BorisFR/FourthInARow/modelisation/openscad Boris/dxf/grille_led.dxf

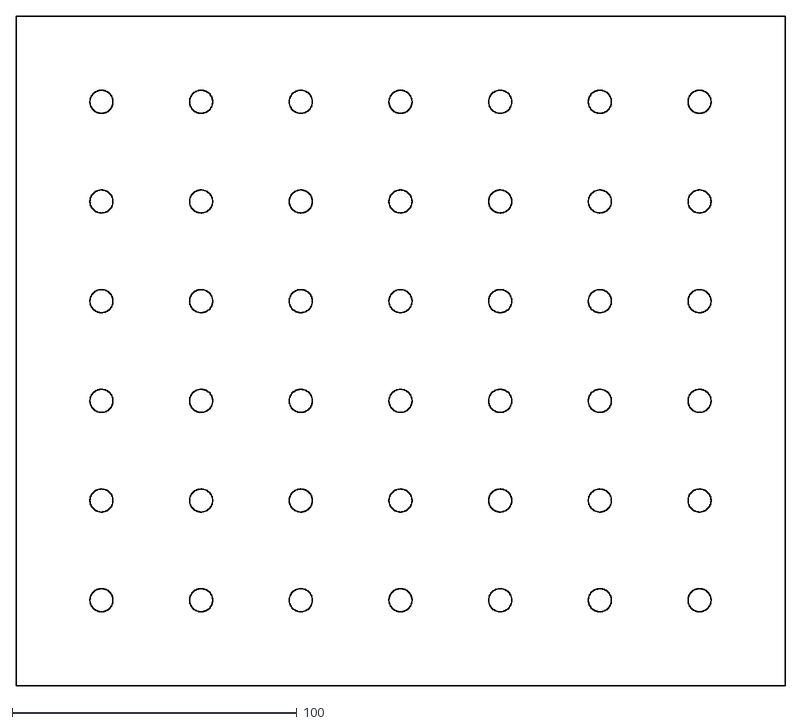
[picture p20: CAD file, 2018-02-16, an earlier design]
modelisation/openscad Boris/dxf/grille_led.dxf
270.0 x 235.0
