BorisFR/FourthInARow/modelisation/openscad Boris/logo_club_forme.scad

// Module names are of the form poly_<inkscape-path-id>().  As a result,
// you can associate a polygon in this OpenSCAD program with the corresponding
// SVG element in the Inkscape document by looking for the XML element with
// the attribute id="inkscape-path-id".

// fudge value is used to ensure that subtracted solids are a tad taller
// in the z dimension than the polygon being subtracted from.  This helps
// keep the resulting .stl file manifold.
fudge = 0.1;

module poly_path4018(h)
{
  scale([25.4/90, -25.4/90, 1]) union()
  {
    linear_extrude(height=h)
      polygon([[90.659249,289.750661],[83.343842,288.992171],[76.579249,287.989571],[70.709028,286.610592],[68.141889,285.798806],[65.829039,284.908071],[62.908844,283.478431],[60.658164,281.934383],[58.979457,280.194394],[57.775179,278.176931],[57.151487,276.374200],[57.165849,274.378051],[57.683533,271.892219],[58.831347,269.317445],[60.700641,266.490165],[63.382769,263.246821],[65.719446,260.991102],[68.435223,258.995745],[71.358545,257.370885],[74.317859,256.226661],[76.376701,255.835436],[78.798217,255.727687],[81.344446,255.900305],[83.777429,256.350181],[86.680459,257.259658],[90.148629,258.548171],[94.282923,260.134263],[95.939330,260.624558],[97.598753,260.954702],[101.757177,261.259585],[108.419249,261.299011],[115.968636,261.189759],[122.575564,260.829745],[129.224336,260.141100],[136.899249,259.045961],[148.563741,256.931576],[159.470724,254.418937],[164.250704,253.113584],[168.373971,251.829042],[171.684745,250.605436],[174.027249,249.482891],[175.594909,248.368684],[177.086468,246.950220],[178.374152,245.365561],[179.330189,243.752771],[180.052963,241.887816],[180.438091,240.013463],[180.473573,238.080083],[180.147404,236.038042],[179.447584,233.837711],[178.362110,231.429458],[176.878979,228.763651],[174.986189,225.790661],[172.495477,222.231457],[169.781913,218.710319],[166.712616,215.088056],[163.154702,211.225476],[158.975290,206.983389],[154.041499,202.222603],[141.379249,190.588171],[130.193118,180.442460],[122.048123,172.813290],[114.975124,165.806894],[107.004979,157.529511],[92.708942,142.381291],[89.394781,138.695880],[87.069869,135.903401],[84.101231,131.984351],[81.236209,127.769048],[78.493955,123.293912],[75.893621,118.595362],[73.454356,113.709819],[71.195314,108.673703],[69.135644,103.523433],[67.294499,98.295431],[64.587242,89.359380],[61.715809,78.946991],[57.426673,61.076893],[53.704769,43.550671],[50.494949,28.021741],[48.968799,20.854952],[47.926591,14.491880],[47.329637,8.644340],[47.139249,3.024151],[47.221507,-0.681781],[47.470524,-4.126965],[47.889664,-7.344962],[48.482289,-10.369329],[49.167555,-12.973382],[49.979547,-15.416424],[50.916883,-17.695960],[51.978182,-19.809490],[53.162061,-21.754519],[54.467140,-23.528548],[55.892037,-25.129081],[57.435369,-26.553619],[59.831899,-28.403899],[62.441719,-30.183412],[64.897340,-31.656209],[66.831269,-32.586339],[68.062552,-32.971919],[69.225812,-33.184883],[70.313376,-33.226918],[71.317573,-33.099713],[72.230731,-32.804955],[73.045177,-32.344333],[73.753241,-31.719535],[74.347249,-30.932249],[75.244232,-29.141969],[75.771532,-26.671264],[76.069006,-22.372194],[76.276509,-15.096819],[76.883849,0.903181],[77.572240,8.734361],[78.398460,16.265981],[79.364191,23.507788],[80.471117,30.469525],[81.720918,37.160937],[83.115278,43.591768],[84.655877,49.771765],[86.344399,55.710671],[89.116881,64.178674],[92.094157,71.922100],[95.321193,79.048738],[98.842959,85.666381],[102.053840,90.680658],[107.831329,99.337277],[119.736179,116.670671],[123.070229,121.208504],[126.568351,125.630126],[130.452985,130.170657],[134.946572,135.065216],[140.271552,140.548922],[146.650364,146.856896],[163.459249,162.886121],[172.306503,171.297117],[179.909778,178.727462],[186.415358,185.339241],[191.969524,191.294536],[196.718558,196.755431],[200.808740,201.884010],[204.386354,206.842355],[207.597679,211.792551],[210.071622,216.212622],[212.185068,220.779437],[213.808260,225.181554],[214.811439,229.107531],[215.094776,231.642732],[215.163992,234.597188],[215.024891,237.485184],[214.683279,239.821001],[213.888508,242.552279],[212.740158,245.624268],[211.398081,248.645847],[210.022129,251.225891],[207.874665,254.446833],[205.357213,257.588299],[202.486666,260.635848],[199.279917,263.575041],[195.753858,266.391436],[191.925382,269.070593],[187.811382,271.598072],[183.428749,273.959431],[178.625507,276.219177],[173.496670,278.324314],[168.063187,280.268783],[162.346006,282.046526],[156.366073,283.651484],[150.144338,285.077598],[143.701747,286.318810],[137.059249,287.369061],[128.719403,288.428815],[120.856089,289.147120],[112.734356,289.576762],[103.619249,289.770531],[90.659249,289.750731]]);
    linear_extrude(height=h)
      polygon([[-191.260751,268.290151],[-196.902168,267.581342],[-202.620751,266.533031],[-206.786479,265.378407],[-210.820609,263.885676],[-214.594811,262.108575],[-217.980751,260.100841],[-220.135751,258.376568],[-222.620751,256.033381],[-224.457875,253.986072],[-226.064751,251.833418],[-227.449300,249.556864],[-228.619441,247.137858],[-229.583091,244.557847],[-230.348171,241.798278],[-230.922600,238.840597],[-231.314296,235.666251],[-231.510054,231.855976],[-231.136432,228.306251],[-230.430274,224.556853],[-229.432567,220.434277],[-228.223772,216.241735],[-226.884351,212.282441],[-225.054672,207.859900],[-222.754797,202.927021],[-220.579551,198.768730],[-218.260245,194.754812],[-215.785016,190.869090],[-213.141997,187.095390],[-210.319323,183.417535],[-207.305131,179.819351],[-204.087554,176.284661],[-200.654729,172.797291],[-168.460751,143.098191],[-148.403251,124.658812],[-140.060751,116.816491],[-143.593631,108.533008],[-150.058361,94.110671],[-155.385170,83.070671],[-157.369777,78.894427],[-158.470117,76.043441],[-158.803941,73.799691],[-158.945650,71.083441],[-159.018135,68.821892],[-159.185650,67.671401],[-159.858957,67.063558],[-161.247299,66.145760],[-165.811063,63.571122],[-172.160896,60.329121],[-179.580751,56.801391],[-183.824143,54.676453],[-185.078370,53.811076],[-186.180005,52.820271],[-187.695377,51.078496],[-188.075374,50.318631],[-188.321666,49.446761],[-188.491488,47.983218],[-188.345766,46.506958],[-187.862406,44.910058],[-187.019317,43.084591],[-186.250592,41.876663],[-184.973757,40.312521],[-180.235778,35.364491],[-175.040036,30.368521],[-173.513174,29.208651],[-172.059973,28.394991],[-169.738114,27.452678],[-167.530373,26.858891],[-165.231276,26.676108],[-162.411148,27.013421],[-157.602646,28.053565],[-154.783414,28.921121],[-151.218304,30.196612],[-140.442784,34.500238],[-122.460751,42.022121],[-80.371522,59.632586],[-53.180751,70.832621],[-35.420751,77.897521],[-17.783759,84.775288],[-11.902779,86.916961],[-7.167961,88.498571],[-2.854636,90.011714],[0.754348,91.604912],[3.651700,93.274507],[5.830129,95.016841],[7.362626,96.721747],[8.441829,98.271471],[9.046006,99.909720],[9.208739,102.125191],[9.177520,103.483288],[9.021331,104.534915],[8.666626,105.581679],[8.039859,106.925191],[7.118134,108.538414],[5.950297,110.172950],[4.572139,111.794919],[3.019453,113.370443],[1.328029,114.865646],[-0.466340,116.246648],[-2.327864,117.479573],[-4.220751,118.530541],[-6.855241,119.734950],[-9.175447,120.429288],[-11.818305,120.742915],[-15.420751,120.805191],[-20.179151,120.643697],[-21.723836,120.376770],[-23.420751,119.906091],[-27.096784,118.674275],[-30.845216,117.151826],[-35.089383,115.152190],[-40.252621,112.488811],[-44.893341,110.127679],[-50.630289,107.436042],[-69.340751,99.266731],[-104.510294,84.409603],[-113.057557,81.031994],[-115.492119,80.184023],[-116.860751,79.831121],[-117.568399,79.768900],[-118.085153,79.851620],[-118.547244,80.129472],[-119.090901,80.652651],[-119.590440,81.248016],[-119.895176,81.853772],[-120.159451,83.801391],[-120.047693,86.403385],[-119.455411,89.950671],[-117.817001,98.394281],[-117.043744,101.990445],[-116.330481,104.396591],[-115.525953,105.788028],[-114.533281,106.944551],[-112.867962,108.113303],[-110.699113,108.945046],[-107.549216,109.570621],[-102.940751,110.120871],[-93.863695,111.199373],[-84.269111,112.628370],[-74.690974,114.320922],[-65.663261,116.190091],[-57.409072,118.236127],[-50.829173,120.304072],[-48.100953,121.370200],[-45.711951,122.470531],[-43.635714,123.614643],[-41.845791,124.812111],[-39.027702,127.203567],[-36.566451,129.894250],[-34.584037,132.732365],[-33.202461,135.566121],[-32.642605,137.509333],[-32.279758,139.708807],[-32.141060,141.925556],[-32.253651,143.920591],[-32.686019,145.954015],[-33.346471,148.076651],[-34.364692,150.348992],[-35.658884,152.615242],[-37.052945,154.597124],[-38.370771,156.016361],[-39.826912,157.022448],[-41.475361,157.855661],[-42.525818,158.215924],[-43.615796,158.430717],[-46.940751,158.555271],[-50.375507,158.394233],[-53.197161,157.857161],[-57.309769,156.517611],[-61.772877,154.618911],[-66.452115,152.224168],[-71.213111,149.396491],[-73.828489,147.827155],[-76.388858,146.541945],[-79.413264,145.306600],[-83.420751,143.886861],[-89.504063,141.978396],[-94.830043,140.713768],[-100.023383,139.973942],[-105.708771,139.639881],[-111.270931,139.613212],[-115.148771,140.014831],[-118.016579,140.599324],[-120.890771,141.390535],[-123.579757,142.328901],[-125.891951,143.354861],[-129.715751,145.683911],[-135.247086,150.458556],[-147.297728,161.274092],[-181.482809,192.466021],[-191.124186,201.497127],[-196.304857,206.646541],[-198.408734,209.300108],[-200.235262,211.911253],[-201.767386,214.442277],[-202.988054,216.855481],[-203.880213,219.113164],[-204.426808,221.177629],[-204.610787,223.011174],[-204.415097,224.576101],[-204.062810,225.555784],[-203.574535,226.418130],[-202.942265,227.168638],[-202.157994,227.812808],[-201.213713,228.356142],[-200.101418,228.804141],[-197.340751,229.436131],[-192.786635,229.899863],[-185.908948,230.348257],[-169.526156,230.960931],[-161.529488,231.008047],[-154.331865,230.824040],[-147.807448,230.403368],[-141.830399,229.740491],[-137.945434,229.330632],[-134.611609,229.252555],[-131.707652,229.509741],[-129.112291,230.105671],[-127.194219,230.879766],[-125.594231,231.810731],[-124.341773,233.060040],[-123.260751,234.602051],[-122.711321,235.687118],[-122.426157,236.747628],[-122.304731,241.150661],[-122.442949,245.535166],[-122.666670,247.012659],[-123.041751,248.496231],[-123.891148,250.925278],[-124.903971,253.190691],[-126.267691,255.278678],[-128.047507,257.258537],[-130.059780,258.952363],[-132.120871,260.182251],[-135.192413,261.263197],[-139.740751,262.546921],[-145.551680,263.944120],[-151.303992,265.158679],[-156.976863,266.187783],[-162.549469,267.028617],[-168.000985,267.678364],[-173.310586,268.134209],[-178.457450,268.393337],[-183.420751,268.452931],[-191.260751,268.290151]]);
    linear_extrude(height=h)
      polygon([[-4.605071,78.609521],[-6.086199,77.715177],[-7.544956,76.464570],[-8.858130,74.979308],[-9.902511,73.381001],[-11.292486,69.823331],[-13.492731,63.390671],[-16.877551,53.520490],[-18.587616,49.095412],[-20.552451,44.459693],[-25.975435,32.904386],[-34.604511,15.550671],[-41.869837,0.909671],[-45.804901,-7.329329],[-49.076931,-15.784419],[-51.468055,-22.948140],[-53.562062,-30.245613],[-55.360248,-37.684160],[-56.863911,-45.271105],[-58.074346,-53.013772],[-58.992849,-60.919482],[-59.620719,-68.995561],[-59.959251,-77.249329],[-59.986778,-84.896922],[-59.641792,-91.334432],[-58.872601,-97.129390],[-57.627511,-102.849329],[-56.792764,-105.788147],[-55.796079,-108.717054],[-54.647718,-111.614782],[-53.357944,-114.460067],[-51.937022,-117.231640],[-50.395213,-119.908236],[-48.742782,-122.468588],[-46.989991,-124.891429],[-44.804214,-127.602145],[-42.502594,-130.178271],[-40.065854,-132.636464],[-37.474719,-134.993385],[-34.709917,-137.265694],[-31.752171,-139.470050],[-28.582207,-141.623111],[-25.180751,-143.741539],[-20.465883,-146.386236],[-15.701538,-148.719449],[-10.926690,-150.728782],[-6.180311,-152.401843],[-1.501373,-153.726235],[3.071149,-154.689565],[7.498284,-155.279438],[11.741059,-155.483459],[16.306525,-155.243490],[20.930606,-154.509804],[25.607775,-153.284681],[30.332508,-151.570403],[35.099278,-149.369251],[39.902559,-146.683505],[44.736824,-143.515448],[49.596549,-139.867359],[54.925458,-135.204368],[60.835269,-129.382949],[66.525721,-123.229228],[71.196549,-117.569329],[73.849417,-113.774652],[76.345202,-109.647828],[78.518977,-105.481754],[80.205819,-101.569329],[81.527524,-97.393061],[82.389917,-93.188595],[82.762084,-89.162032],[82.613109,-85.519469],[82.129858,-82.877307],[81.359581,-80.279073],[80.343643,-77.841405],[79.123409,-75.680939],[77.080796,-73.115053],[74.274899,-70.135939],[71.264714,-67.417474],[70.098936,-66.579631],[69.053189,-66.005389],[67.243982,-65.339469],[66.567263,-65.347863],[65.720089,-65.538689],[64.300099,-66.086751],[62.860802,-67.016556],[61.342854,-68.403272],[59.686912,-70.322065],[57.833630,-72.848102],[55.723666,-76.056549],[50.496309,-84.821339],[46.447898,-91.634132],[43.035341,-96.724849],[39.703215,-100.852634],[35.896099,-104.776629],[32.204144,-108.100959],[28.479516,-110.954840],[24.513967,-113.484049],[20.099249,-115.834359],[17.328969,-117.105719],[14.502480,-118.231419],[11.629355,-119.209003],[8.719168,-120.036014],[5.781491,-120.709995],[2.825897,-121.228489],[-0.138041,-121.589040],[-3.100751,-121.789189],[-7.399868,-121.828043],[-8.849163,-121.650264],[-10.400151,-121.303159],[-12.888981,-120.527360],[-15.138291,-119.606969],[-17.256247,-118.282555],[-19.429291,-116.535389],[-20.757486,-115.193658],[-21.980276,-113.723932],[-23.100110,-112.121643],[-24.119434,-110.382225],[-25.866348,-106.473731],[-27.240601,-101.961909],[-28.026349,-98.168683],[-28.581876,-94.050575],[-28.911802,-89.562667],[-29.020751,-84.660039],[-28.900709,-79.239432],[-28.551553,-73.663702],[-27.989739,-68.133463],[-27.231721,-62.849329],[-25.665164,-54.926970],[-24.703434,-51.239509],[-23.549146,-47.514193],[-22.147104,-43.585769],[-20.442115,-39.288984],[-15.902521,-28.929329],[-5.117601,-4.289329],[6.805266,23.126368],[13.381659,37.790671],[15.411253,42.365671],[16.840809,45.950671],[17.402922,47.675374],[17.702429,49.145085],[17.843359,53.950671],[17.710072,58.676031],[17.449848,60.098669],[16.977609,61.630671],[15.934452,64.199505],[14.642549,66.780751],[13.434713,68.714594],[12.035243,70.621031],[10.494016,72.451261],[8.860911,74.156486],[7.185804,75.687906],[5.518573,76.996721],[3.909096,78.034133],[2.407249,78.751341],[0.615696,79.241194],[-1.192469,79.379993],[-2.953855,79.169011],[-4.605071,78.609521]]);
    difference()
    {
       linear_extrude(height=h)
         polygon([[-224.743971,45.496561],[-225.730726,44.549601],[-226.615404,43.079426],[-227.290653,41.309041],[-227.649120,39.461451],[-227.677809,38.038916],[-227.531465,36.419854],[-226.748706,32.718738],[-225.370898,28.611284],[-223.468094,24.350671],[-209.559448,-2.952169],[-197.020751,-27.768439],[-197.715525,-28.033397],[-199.385941,-28.342619],[-201.341331,-28.731345],[-202.871243,-29.255605],[-203.891111,-29.877391],[-204.316370,-30.558689],[-202.013947,-35.759227],[-195.855681,-48.959066],[-177.011335,-88.766038],[-157.862776,-128.798390],[-151.324242,-142.279955],[-148.489445,-147.874909],[-147.420632,-149.182662],[-146.398466,-150.212629],[-145.087729,-151.145654],[-143.562060,-151.951152],[-141.943045,-152.573900],[-140.352268,-152.958679],[-138.377525,-153.089687],[-136.148111,-152.775389],[-133.770651,-152.289589],[-116.715021,-185.828189],[-104.074947,-210.520002],[-97.565111,-222.788304],[-94.336083,-227.691004],[-90.842982,-232.525153],[-87.112271,-237.261043],[-83.170412,-241.868965],[-79.043868,-246.319210],[-74.759101,-250.582070],[-70.342574,-254.627836],[-65.820751,-258.426799],[-59.613661,-263.146035],[-53.257027,-267.446896],[-46.662255,-271.385748],[-39.740751,-275.018952],[-34.871503,-277.330345],[-30.348153,-279.288701],[-25.881102,-281.012634],[-21.180751,-282.620760],[-14.250888,-284.729735],[-7.580751,-286.338521],[-2.505287,-287.363410],[2.646824,-288.223332],[7.864958,-288.917397],[13.138489,-289.444716],[18.456794,-289.804399],[23.809247,-289.995556],[29.185224,-290.017298],[34.574099,-289.868734],[41.352812,-289.458576],[47.822455,-288.825621],[54.022125,-287.961703],[59.990919,-286.858656],[65.767933,-285.508314],[71.392261,-283.902511],[76.903001,-282.033080],[82.339249,-279.891855],[86.656177,-277.946230],[90.896381,-275.782232],[95.038663,-273.414052],[99.061823,-270.855881],[102.944661,-268.121911],[106.665978,-265.226332],[110.204574,-262.183334],[113.539249,-259.007109],[116.550592,-255.867915],[119.361790,-252.691386],[121.994030,-249.447542],[124.468499,-246.106404],[126.806384,-242.637993],[129.028871,-239.012328],[131.157147,-235.199431],[133.212399,-231.169321],[136.905039,-223.009321],[139.230944,-216.540890],[141.332281,-209.618465],[143.134084,-202.511467],[144.561389,-195.489319],[145.798377,-186.998898],[146.680058,-177.743298],[147.174085,-168.165458],[147.248109,-158.708319],[147.139249,-151.847319],[150.339249,-150.427179],[169.087938,-141.851996],[186.547542,-133.375960],[201.767567,-125.475387],[208.240708,-121.889746],[213.797519,-118.626589],[219.556203,-114.943436],[224.988788,-111.174830],[229.232659,-107.944682],[230.639259,-106.726500],[231.425199,-105.876899],[231.639047,-105.507503],[231.672977,-105.204359],[231.126069,-104.435279],[230.235684,-103.777069],[229.141329,-103.308339],[227.935459,-103.147910],[226.839509,-103.551939],[222.458259,-106.637289],[218.063311,-109.820345],[213.062178,-113.189157],[207.486535,-116.725095],[201.368054,-120.409525],[187.629280,-128.149338],[172.099249,-136.259539],[155.777958,-144.248669],[149.754838,-147.045013],[147.081489,-148.129329],[146.802770,-147.800001],[146.572873,-147.027932],[146.458789,-146.136991],[146.527509,-145.451049],[147.596514,-144.765032],[149.950389,-143.679309],[159.840611,-139.321519],[170.713751,-134.189835],[181.182424,-128.957968],[189.859249,-124.299629],[198.337718,-119.316032],[205.808769,-114.529724],[212.485061,-109.797634],[218.579249,-104.976689],[220.653822,-103.147552],[221.681014,-101.908715],[221.846033,-101.427836],[221.802236,-100.995141],[221.158899,-100.141789],[220.414041,-99.680990],[219.606639,-99.489329],[219.003787,-99.658163],[218.041009,-100.157749],[215.106989,-102.107679],[207.869755,-107.094366],[199.787654,-112.288940],[191.143654,-117.515107],[182.220719,-122.596569],[168.877156,-129.642478],[162.336205,-132.841389],[155.667219,-135.932379],[145.297368,-140.499718],[142.855527,-141.447853],[141.964339,-141.621069],[141.885939,-141.310209],[147.779279,-138.548559],[157.251366,-133.937820],[168.259279,-128.030189],[177.856868,-122.581655],[188.384224,-116.409429],[197.078821,-111.155631],[201.178129,-108.462379],[201.525668,-107.974727],[201.547964,-107.561975],[201.264470,-107.276164],[200.694639,-107.169329],[199.093859,-107.861553],[196.153519,-109.525829],[184.216602,-116.267154],[166.944468,-125.572319],[150.391620,-134.226664],[144.276960,-137.305198],[140.612559,-139.015529],[136.965839,-140.503379],[134.112269,-140.076349],[132.100097,-139.680767],[131.269489,-139.329329],[134.170442,-137.736792],[141.129809,-134.357289],[153.715281,-128.179849],[164.635456,-122.300828],[174.232294,-116.525987],[178.641326,-113.616935],[182.847759,-110.661089],[187.117717,-107.500487],[190.513552,-104.807439],[193.576218,-102.132324],[196.846669,-99.025519],[199.757962,-96.082595],[201.995706,-93.616494],[203.432083,-91.777004],[203.939279,-90.713909],[203.800537,-90.290119],[203.466959,-90.007989],[202.120602,-90.397285],[199.546959,-91.587799],[192.556073,-94.903577],[190.198273,-95.841030],[189.173099,-96.051149],[189.138657,-95.323038],[189.409899,-93.926549],[189.705382,-92.474177],[189.729139,-91.611709],[189.437507,-91.299278],[188.974799,-91.169329],[187.156223,-92.028744],[183.604749,-94.094999],[176.859679,-98.121401],[169.909150,-102.079851],[162.768304,-105.962665],[155.452283,-109.762158],[147.976228,-113.470643],[140.355282,-117.080435],[132.604585,-120.583849],[124.739279,-123.973199],[112.257107,-129.029650],[107.629033,-130.788678],[105.651889,-131.420189],[107.009628,-130.510827],[110.717619,-128.472339],[117.698561,-124.671277],[122.737389,-121.671554],[125.791747,-119.500236],[126.561514,-118.733687],[126.819279,-118.184389],[126.763954,-117.843093],[126.408163,-117.757600],[125.467186,-118.070410],[123.656302,-118.924020],[116.285930,-122.823637],[102.019279,-130.596439],[89.219279,-137.587009],[80.419279,-140.437169],[64.728407,-145.384138],[50.400989,-149.548129],[36.946143,-153.153470],[22.722583,-156.676173],[8.242791,-159.994102],[-5.980751,-162.985119],[-19.512157,-165.534860],[-34.118172,-168.021905],[-48.255476,-170.195985],[-60.380751,-171.806829],[-66.700751,-172.623099],[-67.209251,-172.863373],[-67.420751,-173.218629],[-58.740624,-195.840173],[-49.739911,-218.449322],[-49.190588,-218.745739],[-47.924589,-218.814230],[-41.660321,-218.223136],[-36.508446,-217.537577],[-31.045423,-216.630998],[-25.268531,-215.502764],[-19.175047,-214.152238],[-6.027415,-210.781765],[8.419249,-206.514487],[19.235007,-203.012248],[30.378827,-199.158708],[41.863338,-194.948872],[53.701171,-190.377745],[65.904953,-185.440334],[78.487314,-180.131642],[91.460883,-174.446676],[104.838289,-168.380439],[112.982072,-164.702477],[116.470349,-163.273749],[116.528399,-163.499695],[116.425049,-163.799929],[115.112909,-164.622751],[111.859096,-166.327222],[101.324892,-171.514144],[88.419319,-177.626761],[76.739259,-182.931139],[64.605827,-188.120611],[52.714715,-192.954539],[41.072397,-197.430661],[29.685346,-201.546714],[18.560033,-205.300434],[7.702933,-208.689560],[-2.879483,-211.711828],[-13.180741,-214.364976],[-21.801165,-216.364172],[-29.685213,-217.986226],[-37.070988,-219.276552],[-44.196591,-220.280560],[-46.988388,-220.711091],[-48.342151,-221.082733],[-48.470427,-221.662052],[-48.171391,-222.770883],[-47.670911,-224.129321],[-44.825821,-224.089021],[-41.933676,-223.931103],[-38.271939,-223.529554],[-28.700741,-222.003459],[-16.972318,-219.584230],[-4.531315,-216.465198],[8.533952,-212.676594],[22.135166,-208.248652],[36.184007,-203.211604],[50.592160,-197.595680],[65.271307,-191.431115],[80.133129,-184.748139],[102.823929,-173.726979],[116.338299,-166.968309],[116.112379,-169.468819],[115.683527,-172.972467],[114.999314,-177.168830],[113.250399,-185.482229],[112.026848,-189.863485],[110.518139,-194.537691],[108.880911,-199.047564],[107.271799,-202.935825],[104.778906,-208.009948],[101.907077,-213.067991],[98.820976,-217.838326],[95.685269,-222.049322],[92.558750,-225.657479],[88.997893,-229.320774],[85.204219,-232.842340],[81.379249,-236.025311],[75.961516,-239.795652],[69.859249,-243.421260],[64.142880,-246.238167],[58.093947,-248.734458],[51.746429,-250.901762],[45.134306,-252.731711],[38.291556,-254.215935],[31.252159,-255.346064],[24.050094,-256.113729],[16.719339,-256.510559],[10.639326,-256.557657],[6.159339,-256.316220],[0.445535,-255.568102],[-5.262296,-254.544004],[-10.932126,-253.253569],[-16.531929,-251.706440],[-22.029680,-249.912260],[-27.393351,-247.880671],[-32.590917,-245.621317],[-37.590351,-243.143839],[-41.980407,-240.715981],[-46.182717,-238.167374],[-50.216020,-235.483711],[-54.099054,-232.650682],[-57.850559,-229.653978],[-61.489273,-226.479290],[-65.033934,-223.112309],[-68.503281,-219.538726],[-72.184086,-215.414461],[-75.679057,-211.122527],[-78.993252,-206.655056],[-82.131733,-202.004182],[-85.099560,-197.162039],[-87.901794,-192.120758],[-90.543494,-186.872474],[-93.029721,-181.409319],[-97.808525,-171.449987],[-110.306365,-146.236039],[-166.585193,-33.729329],[-191.103189,15.529861],[-194.455183,22.104948],[-197.957511,27.895282],[-201.646553,32.955755],[-203.572460,35.229448],[-205.558687,37.341261],[-207.948654,39.570993],[-210.415969,41.544053],[-212.839153,43.171022],[-215.096729,44.362481],[-216.820404,44.978156],[-218.949134,45.541081],[-221.049293,45.951456],[-222.687260,46.109481],[-223.725984,45.929186],[-224.743971,45.496561]]);
       translate([0, 0, -fudge])
         linear_extrude(height=h+2*fudge)
           polygon([[-33.807201,-175.619209],[-31.996744,-176.539274],[-30.134471,-177.815589],[-27.925699,-179.894569],[-26.129327,-182.247780],[-24.730847,-184.897941],[-23.715751,-187.867769],[-23.336818,-190.105987],[-23.180122,-192.811205],[-23.253003,-195.510092],[-23.562801,-197.729322],[-24.026418,-199.278867],[-24.669641,-200.811841],[-25.468185,-202.295081],[-26.397766,-203.695423],[-27.434098,-204.979704],[-28.552896,-206.114761],[-29.729875,-207.067430],[-30.940751,-207.804548],[-32.599198,-208.482311],[-34.408104,-208.934674],[-36.256526,-209.141636],[-38.033521,-209.083197],[-39.875374,-208.664878],[-41.896376,-207.868133],[-43.876653,-206.795676],[-45.596331,-205.550221],[-46.733962,-204.404275],[-47.938267,-202.898937],[-49.084524,-201.204016],[-50.048011,-199.489322],[-50.763367,-197.685098],[-51.314508,-195.538123],[-51.669476,-193.206361],[-51.796311,-190.847779],[-51.709434,-188.806070],[-51.447158,-186.865798],[-51.012637,-185.034560],[-50.409024,-183.319957],[-49.639476,-181.729586],[-48.707146,-180.271047],[-47.615190,-178.951938],[-46.366761,-177.779859],[-45.081248,-176.806861],[-43.807503,-176.024750],[-42.538127,-175.429519],[-41.265721,-175.017159],[-39.630513,-174.814404],[-37.623153,-174.864854],[-35.572447,-175.141969],[-33.807201,-175.619209]]);
    }
  }
}

module poly_path4016(h)
{
  scale([25.4/90, -25.4/90, 1]) union()
  {
    linear_extrude(height=h)
      polygon([[92.336789,289.612161],[83.786559,288.919328],[79.854224,288.389784],[76.171706,287.742383],[72.754976,286.980297],[69.620009,286.106697],[66.782776,285.124755],[64.259249,284.037641],[62.305107,282.960498],[60.679856,281.766676],[59.361251,280.437104],[58.327049,278.952711],[57.561084,277.214293],[57.382249,275.154081],[57.503159,273.389065],[57.897058,271.721297],[58.603953,270.029066],[59.663849,268.190661],[61.187796,266.061045],[63.027008,263.873007],[64.957066,261.875733],[66.753549,260.318411],[68.942881,258.866346],[71.383949,257.590728],[73.836493,256.602702],[76.060249,256.013411],[79.021550,255.795483],[82.260402,256.148083],[85.879207,257.090548],[89.980369,258.642211],[93.033073,259.803155],[96.086069,260.769961],[97.983514,261.235782],[99.914424,261.481182],[107.779249,261.581611],[115.339166,261.448566],[122.267964,261.032378],[129.432406,260.259997],[137.699249,259.058371],[144.343637,257.928169],[150.568689,256.703668],[156.439021,255.371209],[162.019249,253.917131],[168.805414,251.809486],[173.496979,249.972231],[175.098870,248.927488],[176.729524,247.476427],[178.196979,245.812083],[179.309269,244.127491],[179.872181,242.985176],[180.217978,241.983721],[180.518579,239.381641],[180.480222,236.732513],[179.853069,234.358951],[178.934661,232.162854],[177.612436,229.659175],[175.923105,226.899432],[173.903376,223.935146],[169.019554,217.599027],[163.254639,211.062981],[159.290784,207.001220],[154.310347,202.187003],[140.419249,189.468551],[126.386722,176.611773],[116.072109,166.701161],[104.199269,154.328173],[92.457199,141.861511],[89.535630,138.589689],[86.902554,135.418355],[84.480378,132.250198],[82.191509,128.987911],[80.042806,125.662305],[78.030953,122.257101],[74.002809,114.472301],[70.646489,106.955671],[67.727269,99.070671],[66.075063,93.902727],[64.285967,87.762436],[60.511834,73.428333],[56.834316,57.795400],[53.682859,42.590671],[50.640309,27.870671],[48.894631,19.543038],[47.802089,12.123281],[47.526989,7.787609],[47.466777,2.496498],[47.612518,-2.658986],[47.955279,-6.587779],[48.517663,-9.724822],[49.242946,-12.651790],[50.133188,-15.373047],[51.190446,-17.892958],[52.416778,-20.215889],[53.814244,-22.346204],[55.384902,-24.288269],[57.130809,-26.046449],[59.382832,-27.895451],[61.989997,-29.738223],[64.542003,-31.303711],[66.628549,-32.320859],[68.422191,-32.842560],[70.105877,-33.032438],[71.556204,-32.888676],[72.649769,-32.409459],[73.479124,-31.653914],[74.239934,-30.693830],[74.876305,-29.610936],[75.332339,-28.486959],[75.662804,-24.752235],[75.948599,-17.089319],[76.361076,-4.621664],[77.085679,5.470681],[78.214330,16.231816],[79.734777,26.981583],[81.572882,37.255899],[83.654509,46.590681],[86.177011,55.677106],[89.123877,64.564837],[92.369884,72.905490],[95.789809,80.350681],[97.708340,83.933106],[100.202739,88.074130],[108.882869,101.151761],[118.935199,115.776403],[124.689519,123.550681],[128.810961,128.628215],[135.108339,135.488761],[139.817307,140.357524],[146.571793,147.022591],[168.091629,167.564341],[175.958139,175.087306],[182.604899,181.643992],[188.114450,187.317435],[192.569329,192.190671],[198.743623,199.518812],[203.759356,206.163223],[207.781122,212.357736],[209.470705,215.359352],[210.973519,218.336181],[212.937571,222.992271],[214.262247,227.383871],[214.957991,231.555249],[215.073278,233.572188],[215.035249,235.550671],[214.804254,238.035479],[214.368332,240.323251],[213.641189,242.764885],[212.536529,245.711281],[210.754096,249.626408],[208.626087,253.182435],[205.985066,256.625059],[202.663599,260.199981],[198.724712,263.851374],[194.532057,267.135471],[189.901270,270.184601],[184.647989,273.131091],[178.370546,276.151411],[171.714244,278.845461],[164.624165,281.233541],[157.045389,283.335951],[151.780705,284.569274],[146.340640,285.672054],[140.715451,286.645580],[134.895396,287.491137],[122.631708,288.803492],[109.471629,289.619411],[100.475089,289.886612],[92.336789,289.612411]]);
    linear_extrude(height=h)
      polygon([[-188.060751,268.310661],[-193.747573,267.812839],[-198.975874,267.059916],[-203.705186,266.059013],[-207.895048,264.817251],[-210.715863,263.750692],[-213.285715,262.594763],[-215.681660,261.311616],[-217.980751,259.863401],[-219.989289,258.298474],[-222.167586,256.280891],[-224.187114,254.136377],[-225.719345,252.190661],[-227.497157,249.146890],[-228.988122,245.708090],[-230.156224,241.971455],[-230.965445,238.034181],[-231.224055,234.919455],[-231.162353,231.303338],[-230.799038,227.511763],[-230.152810,223.870661],[-229.209928,220.146631],[-228.032773,216.210842],[-226.702123,212.315540],[-225.298759,208.712971],[-222.649425,202.987355],[-219.458570,197.072736],[-215.939077,191.338656],[-212.303827,186.154661],[-207.840335,180.685792],[-202.564005,174.833261],[-192.054081,164.979217],[-170.300751,144.991151],[-140.176261,117.228551],[-140.092692,116.724291],[-140.346328,115.726033],[-142.209996,111.230671],[-149.684600,94.622953],[-154.778258,84.030671],[-156.841671,79.910235],[-158.031587,76.942345],[-158.589982,74.358617],[-158.758834,71.390671],[-158.817804,67.710671],[-160.373413,66.534351],[-163.094498,64.899089],[-167.969848,62.307140],[-179.880748,56.472461],[-183.959864,54.426611],[-185.217660,53.607733],[-186.176447,52.795121],[-187.279852,51.503098],[-187.983045,50.140791],[-188.306147,48.652311],[-188.269279,46.981771],[-188.076424,45.880473],[-187.736460,44.810802],[-187.204210,43.709523],[-186.434497,42.513401],[-184.001975,39.583689],[-180.077477,35.515791],[-174.704070,30.336362],[-173.156164,29.171102],[-171.641055,28.337391],[-169.113155,27.308712],[-167.947394,27.090695],[-166.484745,26.974451],[-164.799130,26.959539],[-163.013263,27.097223],[-158.931341,27.883766],[-153.820122,29.440859],[-147.260751,31.875281],[-120.700751,42.910511],[-79.385372,60.194236],[-52.380751,71.321961],[-36.960021,77.451601],[-18.926588,84.492830],[-7.571861,88.529641],[-2.794117,90.239427],[0.841459,91.794121],[3.920040,93.661855],[6.344407,95.758310],[7.293136,96.873203],[8.056562,98.022350],[8.627437,99.198110],[8.998509,100.392841],[9.141540,101.956124],[8.955188,103.729961],[8.464529,105.580117],[7.694639,107.372361],[5.976402,109.789479],[3.310066,112.680671],[0.330149,115.413875],[-2.328831,117.357031],[-4.683302,118.591504],[-7.077554,119.562026],[-9.519235,120.269551],[-12.015998,120.715031],[-14.575492,120.899419],[-17.205367,120.823668],[-19.913273,120.488731],[-22.706861,119.895561],[-26.504297,118.772270],[-30.638112,117.114865],[-36.144773,114.459694],[-44.060751,110.343111],[-55.756169,105.016208],[-76.647938,95.981853],[-98.529164,86.745640],[-113.192951,80.813161],[-117.463671,79.390671],[-118.076073,79.627867],[-118.891291,80.198161],[-119.710599,81.202487],[-120.205991,82.661231],[-120.403386,84.002483],[-120.365702,85.524260],[-119.411641,90.910671],[-117.993851,98.341421],[-117.332649,101.520908],[-116.662981,103.898151],[-115.856327,105.522470],[-114.754318,106.894065],[-113.375953,107.994007],[-111.740231,108.803371],[-109.200878,109.432261],[-105.543501,109.970311],[-94.737573,111.277855],[-84.633313,112.744661],[-75.133460,114.386150],[-66.140751,116.217741],[-59.147904,117.929825],[-52.897716,119.796536],[-47.741035,121.701857],[-45.682401,122.632741],[-44.028711,123.529771],[-41.945400,124.927841],[-40.021066,126.479957],[-38.270866,128.166887],[-36.709958,129.969401],[-35.353499,131.868267],[-34.216646,133.844255],[-33.314558,135.878133],[-32.662391,137.950671],[-32.327158,140.113270],[-32.306883,142.509067],[-32.591060,144.945666],[-33.169181,147.230671],[-34.056827,149.377538],[-35.273626,151.687097],[-36.616799,153.808378],[-37.883571,155.390411],[-39.236368,156.487341],[-40.839441,157.426381],[-41.882899,157.852599],[-42.943241,158.121941],[-46.140751,158.373291],[-49.527409,158.331390],[-52.523071,157.813381],[-56.789655,156.521871],[-61.448866,154.597516],[-66.397952,152.087733],[-71.534161,149.039941],[-75.051332,147.073322],[-79.150981,145.236185],[-83.682281,143.569617],[-88.494407,142.114702],[-93.436533,140.912526],[-98.357832,140.004176],[-103.107480,139.430735],[-107.534651,139.233291],[-110.812505,139.350240],[-114.019726,139.689119],[-117.129760,140.242101],[-120.116053,141.001360],[-122.952053,141.959068],[-125.611207,143.107398],[-128.066960,144.438525],[-130.292761,145.944621],[-136.624340,151.484560],[-149.792711,163.344001],[-182.490812,193.209581],[-191.866946,202.027866],[-196.788591,206.969581],[-199.124200,210.041918],[-201.054139,212.927410],[-202.576017,215.619739],[-203.687440,218.112590],[-204.386017,220.399643],[-204.669355,222.474583],[-204.535064,224.331091],[-203.980751,225.962851],[-203.058909,227.271517],[-201.615567,228.272361],[-199.969292,228.986880],[-198.321487,229.466731],[-194.755459,229.869801],[-188.560953,230.321235],[-172.860751,231.079431],[-164.838708,231.208571],[-156.883860,231.097746],[-149.837457,230.771490],[-144.540751,230.254341],[-140.970309,229.852475],[-137.104351,229.574951],[-133.042491,229.574524],[-129.818766,230.026438],[-128.459806,230.436867],[-127.236703,230.978194],[-126.124897,231.656356],[-125.099831,232.477291],[-123.991722,233.765888],[-123.128601,235.236841],[-122.774424,236.216117],[-122.559846,237.321125],[-122.404971,241.074181],[-122.516597,245.012812],[-123.081411,248.030661],[-123.717928,250.098606],[-124.503869,252.013587],[-125.434951,253.769943],[-126.506892,255.362013],[-127.715408,256.784136],[-129.056217,258.030651],[-130.525035,259.095896],[-132.117581,259.974211],[-135.023018,261.038077],[-139.555514,262.328841],[-145.140074,263.695475],[-151.201708,264.986951],[-161.488991,266.688182],[-171.420751,267.844711],[-180.446172,268.276766],[-188.060751,268.310661]]);
    linear_extrude(height=h)
      polygon([[-3.458421,78.968361],[-5.804211,77.800911],[-6.894019,76.922246],[-8.102784,75.630287],[-9.242983,74.146623],[-10.127091,72.692841],[-13.910611,61.790671],[-16.738418,53.576242],[-19.039081,47.532201],[-21.668105,41.623054],[-25.113871,34.327696],[-35.704081,12.990671],[-42.286679,-0.303329],[-46.102971,-8.449329],[-48.158584,-13.684808],[-50.044370,-19.005976],[-51.762894,-24.422547],[-53.316719,-29.944238],[-54.708412,-35.580762],[-55.940535,-41.341836],[-57.015653,-47.237173],[-57.936331,-53.276489],[-58.788921,-59.987287],[-59.288007,-65.754209],[-59.522360,-72.035482],[-59.580751,-80.289329],[-59.470784,-91.306194],[-59.257286,-94.056382],[-58.870521,-96.511909],[-57.719792,-101.829120],[-56.249732,-106.872827],[-54.453404,-111.656363],[-52.323871,-116.193060],[-49.854195,-120.496251],[-47.037442,-124.579268],[-43.866672,-128.455444],[-40.334951,-132.138109],[-37.576662,-134.683621],[-34.747229,-137.047058],[-31.763107,-139.294686],[-28.540751,-141.492769],[-23.345956,-144.663329],[-18.099079,-147.436279],[-12.772814,-149.824952],[-7.339851,-151.842679],[-3.484911,-153.016398],[0.372918,-153.961853],[4.231608,-154.678609],[8.089129,-155.166229],[11.079242,-155.358548],[13.933519,-155.321578],[16.875081,-155.043181],[20.127049,-154.511219],[24.560903,-153.449606],[29.025890,-151.946581],[33.523674,-150.001189],[38.055919,-147.612477],[42.624290,-144.779487],[47.230451,-141.501266],[51.876066,-137.776859],[56.562799,-133.605309],[59.866723,-130.309008],[63.809617,-126.079159],[67.622224,-121.763390],[70.535289,-118.209329],[73.516068,-113.990566],[76.243842,-109.526865],[78.544952,-105.124397],[80.245739,-101.089329],[81.544835,-96.780191],[82.337704,-92.559505],[82.612736,-88.517059],[82.358319,-84.742639],[81.866117,-82.354521],[81.102197,-79.948867],[80.123968,-77.679723],[78.988839,-75.701139],[77.131770,-73.398654],[74.490018,-70.619774],[71.792674,-68.089504],[69.768829,-66.532849],[68.229646,-65.824502],[66.819589,-65.588243],[65.409750,-65.824047],[63.871219,-66.531889],[62.715489,-67.340015],[61.464900,-68.507307],[60.093268,-70.070118],[58.574403,-72.064802],[54.990229,-77.495200],[50.502879,-85.089329],[46.748262,-91.466443],[43.634871,-96.198822],[40.636411,-100.023299],[37.226589,-103.676709],[33.210376,-107.456870],[29.247164,-110.613745],[25.071831,-113.338953],[20.419249,-115.824109],[16.746029,-117.476758],[13.307019,-118.819799],[10.056723,-119.806001],[6.416842,-120.688563],[2.629034,-121.415131],[-1.065041,-121.933349],[-4.459467,-122.164084],[-7.500771,-121.967649],[-10.247514,-121.487125],[-12.792981,-120.747644],[-15.131148,-119.751349],[-17.255991,-118.500379],[-19.150034,-117.047154],[-20.836663,-115.405148],[-22.360614,-113.525285],[-23.766621,-111.358489],[-25.223949,-108.492483],[-26.456228,-105.263059],[-27.461768,-101.680660],[-28.238879,-97.755734],[-28.785872,-93.498725],[-29.101054,-88.920077],[-29.182737,-84.030237],[-29.029231,-78.839649],[-28.375921,-69.569349],[-27.142697,-61.526914],[-25.508351,-53.717879],[-24.106140,-48.695508],[-22.329447,-43.586593],[-19.779956,-37.346189],[-16.059351,-28.929349],[-5.894371,-5.729349],[6.006759,21.690256],[12.920029,37.164701],[15.577977,43.280483],[17.108749,47.404701],[17.687884,50.373192],[17.830729,54.110651],[17.692461,57.653702],[17.262779,60.190651],[16.429231,62.596983],[15.203988,65.291240],[13.760321,67.927362],[12.271499,70.159291],[10.224062,72.566556],[7.870607,74.883033],[5.520245,76.828640],[3.482089,78.123291],[1.641351,78.844971],[-0.214538,79.236791],[-1.957241,79.283124],[-3.458421,78.968341]]);
    difference()
    {
       linear_extrude(height=h)
         polygon([[-225.241887,44.944111],[-226.041540,43.875991],[-226.754859,42.590671],[-227.262788,40.892012],[-227.413723,38.551691],[-227.330863,36.709882],[-227.066562,34.790800],[-226.611942,32.768321],[-225.958124,30.616323],[-224.017382,25.819276],[-221.173308,20.190671],[-207.921270,-5.700069],[-199.576375,-22.406175],[-197.577664,-26.646479],[-197.032245,-28.136429],[-199.486281,-28.557129],[-201.056537,-28.808278],[-202.439279,-29.226360],[-203.509855,-29.762877],[-204.143615,-30.369329],[-202.771413,-33.749579],[-198.067507,-43.963739],[-177.003100,-88.449329],[-157.365432,-129.518648],[-148.666649,-147.374679],[-147.585299,-148.712875],[-146.246907,-150.006373],[-144.797317,-151.128794],[-143.382370,-151.953759],[-141.746058,-152.510593],[-139.836819,-152.815042],[-137.826910,-152.852097],[-135.888591,-152.606749],[-134.221278,-152.351400],[-133.810224,-152.427316],[-133.523971,-152.641249],[-117.653351,-183.649319],[-100.297971,-217.729322],[-96.428142,-224.230611],[-91.954931,-230.849321],[-87.278504,-236.825623],[-81.806981,-243.087877],[-76.015087,-249.117988],[-70.377551,-254.397858],[-66.247982,-257.878496],[-61.983186,-261.206341],[-57.596932,-264.372579],[-53.102989,-267.368399],[-48.515128,-270.184987],[-43.847116,-272.813531],[-39.112724,-275.245218],[-34.325721,-277.471236],[-26.656685,-280.562185],[-18.560427,-283.284405],[-10.300574,-285.557383],[-2.140751,-287.300607],[5.084530,-288.425397],[12.503016,-289.228997],[20.040125,-289.711400],[27.621274,-289.872601],[35.171879,-289.712595],[42.617357,-289.231374],[49.883125,-288.428934],[56.894599,-287.305267],[65.368966,-285.424188],[73.699249,-282.962203],[79.575121,-280.846689],[85.140540,-278.500479],[90.425691,-275.905153],[95.460758,-273.042287],[100.275927,-269.893460],[104.901382,-266.440251],[109.367308,-262.664237],[113.703889,-258.546996],[118.070052,-253.924682],[121.922317,-249.289253],[125.472320,-244.367464],[128.931699,-238.886075],[131.767358,-233.795402],[134.384551,-228.422157],[136.774759,-222.791351],[138.929462,-216.927997],[140.840140,-210.857105],[142.498274,-204.603687],[143.895344,-198.192754],[145.022829,-191.649319],[145.923690,-185.137312],[146.458818,-179.500362],[146.731242,-173.217890],[146.843989,-164.769319],[146.930789,-151.809319],[152.154989,-149.474659],[170.027231,-141.263845],[186.819209,-133.071879],[201.527549,-125.479223],[207.085404,-122.407339],[212.259209,-119.380619],[219.522092,-114.803389],[225.648438,-110.545778],[229.880170,-107.166692],[231.048656,-105.981255],[231.459209,-105.225039],[231.226002,-104.622371],[230.590273,-104.083098],[229.647859,-103.665338],[228.494599,-103.427209],[227.667500,-103.404978],[226.871831,-103.662523],[223.939209,-105.748529],[219.690681,-108.820645],[214.044089,-112.634987],[207.865057,-116.620602],[202.019209,-120.206539],[189.379209,-127.405349],[176.964757,-133.944046],[163.108024,-140.876729],[151.708989,-146.296017],[148.149851,-147.842082],[146.667629,-148.294529],[146.414862,-147.713566],[146.348751,-146.687335],[146.459978,-145.643370],[146.739229,-145.009199],[152.824319,-142.245669],[165.281379,-136.655256],[177.232343,-130.835204],[188.318023,-124.967745],[198.179229,-119.235109],[204.465986,-115.207944],[210.534336,-111.010138],[215.945132,-106.957327],[220.259229,-103.365149],[221.265031,-102.438151],[221.733773,-101.867483],[221.782731,-101.423218],[221.529179,-100.875429],[220.885926,-100.133283],[219.798049,-99.866959],[218.614047,-99.953698],[217.568089,-100.497569],[211.522532,-104.801953],[204.778216,-109.287829],[197.496228,-113.861489],[189.837654,-118.429223],[181.963581,-122.897323],[174.035095,-127.172080],[166.213282,-131.159785],[158.659229,-134.766729],[148.282589,-139.371269],[143.530337,-141.315069],[142.270249,-141.716751],[141.743929,-141.742009],[141.560569,-141.301429],[147.779229,-138.380489],[155.734121,-134.532363],[164.516229,-129.931024],[174.289837,-124.487541],[185.219229,-118.112979],[198.139538,-110.316057],[200.669345,-108.629361],[201.379229,-107.911979],[201.180563,-107.413497],[200.576212,-107.349374],[199.553650,-107.721984],[198.100349,-108.533699],[186.021292,-115.428669],[168.363152,-124.993012],[151.233330,-133.971361],[144.775102,-137.223486],[140.739229,-139.108349],[136.899229,-140.700379],[133.773119,-140.193149],[131.592907,-139.740978],[130.753409,-139.366829],[133.830572,-137.721654],[141.079489,-134.214319],[149.936523,-129.923973],[156.879969,-126.396219],[166.897575,-120.804506],[175.773177,-115.341499],[183.686990,-109.890042],[190.819229,-104.332979],[194.122969,-101.436440],[197.494338,-98.226134],[200.481113,-95.149239],[202.631069,-92.652929],[203.713436,-91.060442],[203.776118,-90.662818],[203.590109,-90.363079],[203.253900,-90.179690],[202.708656,-90.252930],[200.258299,-91.396609],[193.595752,-94.578352],[190.764194,-95.800610],[189.353019,-96.289329],[189.040377,-96.212877],[188.927632,-95.867063],[189.283219,-93.668609],[189.518322,-91.927438],[189.351061,-91.525949],[188.907224,-91.450158],[188.121785,-91.709789],[186.929716,-92.314566],[183.065589,-94.598459],[175.276141,-99.204120],[167.348462,-103.658252],[159.254331,-107.974754],[150.965529,-112.167529],[142.453835,-116.250478],[133.691027,-120.237502],[124.648885,-124.142502],[115.299189,-127.979379],[105.944209,-131.604808],[103.971750,-132.237885],[103.608669,-132.278477],[103.640789,-132.142329],[109.859189,-128.743879],[119.600462,-123.358175],[123.467111,-121.044451],[125.673049,-119.559269],[126.333439,-118.841163],[126.392149,-118.231949],[126.353155,-117.996918],[126.208069,-117.888858],[124.309113,-118.712145],[105.042489,-129.125829],[89.505779,-137.574759],[82.802489,-139.821119],[72.351235,-143.214247],[61.538977,-146.512841],[50.425266,-149.701335],[39.069653,-152.764162],[27.531688,-155.685755],[15.870922,-158.450548],[4.146906,-161.042975],[-7.580811,-163.447469],[-21.151443,-165.991012],[-34.906039,-168.330090],[-48.181092,-170.357516],[-60.313091,-171.966099],[-67.105091,-172.931969],[-67.105263,-173.631553],[-66.655721,-175.103269],[-57.230583,-199.292364],[-49.729481,-218.129321],[-48.966537,-218.425953],[-47.305262,-218.509900],[-41.340811,-218.040301],[-32.702588,-216.774392],[-23.109457,-214.881755],[-12.641476,-212.385507],[-1.378702,-209.308766],[10.598809,-205.674648],[23.210999,-201.506271],[36.377811,-196.826752],[50.019189,-191.659209],[63.118805,-186.409946],[77.042244,-180.577658],[91.134156,-174.442301],[104.739189,-168.283829],[115.518721,-163.361043],[116.551514,-163.083119],[116.579189,-163.492079],[116.241332,-163.974935],[115.031569,-164.774682],[108.819189,-168.010209],[97.963541,-173.328023],[87.046819,-178.448421],[76.100367,-183.358303],[65.155531,-188.044566],[54.243656,-192.494109],[43.396087,-196.693831],[32.644170,-200.630629],[22.019249,-204.291402],[9.039238,-208.429315],[-3.487278,-212.039118],[-15.460531,-215.093674],[-26.780751,-217.565843],[-37.186327,-219.420564],[-45.731701,-220.624451],[-47.348134,-220.895320],[-48.213961,-221.241142],[-48.353393,-221.816724],[-48.067861,-222.782950],[-47.276711,-224.119459],[-46.041367,-224.155415],[-43.511861,-223.969571],[-38.515446,-223.383836],[-33.172057,-222.590919],[-21.626894,-220.422061],[-9.241437,-217.540052],[3.619249,-214.021943],[12.528686,-211.292379],[21.703745,-208.259963],[31.113125,-204.936750],[40.725523,-201.334797],[50.509637,-197.466160],[60.434164,-193.342896],[70.467802,-188.977060],[80.579249,-184.380709],[102.595469,-173.680539],[112.122726,-169.006102],[116.245009,-167.160529],[116.393487,-167.473279],[116.377833,-168.392372],[115.732629,-173.569319],[114.689153,-179.712759],[113.235236,-186.087345],[111.465503,-192.322919],[109.474579,-198.049322],[107.238169,-203.300138],[104.603293,-208.608865],[101.749242,-213.637821],[98.855309,-218.049322],[95.095461,-222.918165],[90.961497,-227.569855],[86.605423,-231.844567],[82.179249,-235.582479],[77.710460,-238.823749],[73.024275,-241.791195],[68.111590,-244.488789],[62.963304,-246.920506],[57.570314,-249.090318],[51.923516,-251.002200],[46.013809,-252.660123],[39.832089,-254.068063],[32.341870,-255.333045],[24.294372,-256.270436],[16.682523,-256.787982],[10.499249,-256.793429],[4.195089,-256.244517],[-2.230220,-255.291241],[-8.715509,-253.951459],[-15.199609,-252.243028],[-21.621353,-250.183805],[-27.919570,-247.791648],[-34.033092,-245.084413],[-39.900751,-242.079958],[-43.849334,-239.742406],[-48.408297,-236.789269],[-52.913486,-233.665795],[-56.700751,-230.817232],[-60.891648,-227.150391],[-65.807092,-222.389009],[-70.575515,-217.409761],[-74.325351,-213.089322],[-79.689069,-205.909332],[-84.390351,-198.689322],[-86.683809,-194.674436],[-89.078049,-190.137201],[-91.329338,-185.556026],[-93.193941,-181.409319],[-97.463733,-172.486025],[-109.377619,-148.441269],[-166.097855,-34.982439],[-191.959637,16.874071],[-194.416358,21.640286],[-196.994564,26.068011],[-199.661932,30.105083],[-202.386137,33.699341],[-205.639121,37.260704],[-209.163997,40.374088],[-212.758596,42.879931],[-214.518864,43.855162],[-216.220751,44.618671],[-218.725105,45.385982],[-221.500751,45.707501],[-224.117151,45.718708],[-224.698423,45.463826],[-225.241887,44.944111]]);
       translate([0, 0, -fudge])
         linear_extrude(height=h+2*fudge)
           polygon([[-34.254821,-175.345129],[-32.603316,-176.021159],[-31.131862,-176.897142],[-29.649092,-178.108273],[-27.963641,-179.789749],[-26.810103,-181.141687],[-25.800954,-182.595771],[-24.939095,-184.144346],[-24.227431,-185.779759],[-23.668862,-187.494355],[-23.266290,-189.280480],[-23.022619,-191.130479],[-22.940751,-193.036699],[-23.203437,-196.507111],[-23.534225,-198.110580],[-24.000134,-199.632217],[-24.602785,-201.076517],[-25.343797,-202.447977],[-26.224789,-203.751090],[-27.247381,-204.990352],[-28.924696,-206.575658],[-30.573241,-207.752580],[-32.345848,-208.508692],[-34.321451,-209.082272],[-36.311781,-209.336397],[-38.233288,-209.222827],[-40.203271,-208.723072],[-42.339031,-207.818647],[-44.562889,-206.455161],[-46.659031,-204.527319],[-48.398944,-202.433478],[-49.715041,-200.444177],[-50.665273,-198.267161],[-51.406753,-195.793334],[-51.888805,-193.231279],[-52.060751,-190.789579],[-51.902382,-188.520502],[-51.456518,-186.165515],[-50.767020,-183.903006],[-49.877751,-181.911359],[-48.695977,-180.089070],[-47.243278,-178.420009],[-45.627301,-177.012114],[-43.955691,-175.973319],[-41.478015,-174.972337],[-39.164033,-174.542313],[-36.820662,-174.670745],[-34.254821,-175.345129]]);
    }
  }
}

module poly_path4008(h)
{
  scale([25.4/90, -25.4/90, 1]) union()
  {
    linear_extrude(height=h)
      polygon([[93.059249,288.973671],[86.282426,288.505076],[80.128321,287.763481],[74.639886,286.762192],[69.860072,285.514515],[65.831830,284.033753],[62.598111,282.333213],[61.292620,281.404685],[60.201867,280.426201],[59.331220,279.399425],[58.686049,278.326021],[58.282352,277.247870],[58.064233,276.079792],[58.028751,274.838450],[58.172966,273.540512],[58.493935,272.202642],[58.988718,270.841507],[59.654373,269.473771],[60.487959,268.116101],[62.010650,266.092871],[63.847034,263.962357],[65.694068,262.056627],[67.248709,260.707751],[69.229719,259.418363],[71.411411,258.282943],[73.636514,257.374432],[75.747759,256.765771],[78.252166,256.392662],[80.863379,256.610531],[83.108073,257.052445],[85.624599,257.748847],[88.236435,258.644923],[90.767059,259.685861],[92.994527,260.531845],[95.727059,261.384361],[97.653712,261.871332],[99.603452,262.125252],[107.779249,262.228681],[115.329249,262.106656],[120.899249,261.831241],[127.501031,261.132493],[134.226703,260.253165],[140.848648,259.225762],[147.139249,258.082791],[155.380094,256.262299],[163.407904,254.154683],[170.024612,252.100426],[172.429407,251.199708],[174.032149,250.440011],[175.854941,249.179675],[177.531934,247.653407],[178.953178,245.974943],[180.008719,244.258021],[180.866349,242.081198],[181.174349,239.744971],[181.143022,237.533200],[180.898229,235.572521],[180.301303,233.683090],[179.278041,231.403433],[177.863062,228.802856],[176.090989,225.950661],[173.761716,222.576298],[171.163863,219.159476],[168.241931,215.640390],[164.940421,211.959233],[161.203834,208.056202],[156.976673,203.871490],[146.828629,194.417801],[133.068629,181.967021],[125.827759,175.197786],[118.317999,167.887021],[103.762969,152.936403],[91.499699,139.896651],[87.777623,135.486262],[84.291194,130.858273],[81.036312,126.005361],[78.008873,120.920203],[75.204776,115.595478],[72.619920,110.023862],[70.250201,104.198034],[68.091519,98.110671],[66.031024,91.457674],[63.785896,83.443560],[61.413847,74.283001],[58.972589,64.190671],[56.348243,52.595627],[54.016029,40.830671],[51.314649,27.870671],[49.570654,19.430236],[48.426089,11.710671],[48.198193,7.913551],[48.101869,2.828561],[48.309651,-3.548702],[48.585933,-6.323024],[48.989856,-8.887993],[49.530956,-11.293748],[50.218769,-13.590427],[51.062832,-15.828172],[52.072679,-18.057119],[53.876152,-21.301188],[55.877189,-23.830979],[58.025232,-25.886745],[60.607151,-27.946177],[63.344966,-29.804552],[65.960699,-31.257149],[68.157932,-32.135758],[69.982189,-32.380759],[71.364601,-32.251069],[72.443712,-31.830824],[73.296206,-31.073267],[73.998769,-29.931639],[74.632668,-28.269194],[75.032133,-26.212932],[75.240796,-23.414525],[75.302289,-19.525649],[75.622009,-6.849329],[76.431744,5.691844],[77.709162,17.818896],[79.445071,29.490149],[81.630276,40.663925],[84.255583,51.298543],[87.311799,61.352326],[88.998624,66.148380],[90.789729,70.783595],[92.683964,75.252762],[94.680179,79.550671],[96.787439,83.609236],[99.476418,88.151213],[103.280533,94.032920],[108.733199,102.110671],[119.198109,117.223222],[125.321869,125.460231],[131.122228,132.099853],[139.387506,140.714557],[150.194310,151.381796],[163.619249,164.179021],[175.705020,175.718766],[185.062382,185.067833],[192.368745,192.925710],[198.301519,199.991881],[201.239053,203.817225],[203.867346,207.492475],[206.191385,211.026504],[208.216158,214.428186],[209.946653,217.706393],[211.387858,220.869999],[212.544761,223.927877],[213.422349,226.888901],[214.217848,231.024738],[214.420549,234.924713],[214.027023,238.727200],[213.033839,242.570571],[211.827241,245.671219],[210.234378,248.990293],[208.447039,252.159649],[206.657009,254.811141],[204.485037,257.396013],[201.798427,260.182953],[198.885267,262.889355],[196.033649,265.232611],[191.667181,268.291062],[186.834383,271.194427],[181.537618,273.941389],[175.779249,276.530631],[170.300597,278.659407],[164.480461,280.596565],[158.320819,282.341674],[151.823649,283.894301],[144.990930,285.254012],[137.824638,286.420376],[130.326752,287.392960],[122.499249,288.171331],[109.832274,288.928943],[99.459249,289.257511],[93.059249,288.973671]]);
    linear_extrude(height=h)
      polygon([[-187.420751,267.649921],[-193.677478,267.181379],[-199.466963,266.329998],[-204.783156,265.098147],[-209.620008,263.488195],[-213.971470,261.502508],[-217.831492,259.143457],[-219.575323,257.824659],[-221.194025,256.413408],[-222.686842,254.910000],[-224.053019,253.314731],[-225.483081,251.282121],[-226.834945,248.923153],[-228.024740,246.398956],[-228.968594,243.870661],[-229.638933,241.368037],[-230.160403,238.590208],[-230.498752,235.760558],[-230.619728,233.102471],[-230.418944,229.577326],[-229.833644,225.657878],[-228.892862,221.436211],[-227.625630,217.004406],[-226.060982,212.454545],[-224.227951,207.878711],[-222.155570,203.368985],[-219.872873,199.017451],[-215.984368,192.579106],[-211.718652,186.492473],[-206.977016,180.626570],[-201.660751,174.850411],[-191.025751,164.909505],[-169.500751,145.152621],[-139.625340,117.654381],[-139.334739,117.100868],[-139.519410,116.054280],[-142.312252,109.426921],[-148.689562,95.206395],[-153.906194,84.339441],[-156.220224,79.523806],[-157.502281,76.499441],[-157.927279,74.260275],[-158.121247,71.093771],[-158.193047,67.436881],[-159.220020,66.579501],[-161.316307,65.153480],[-164.832914,63.164876],[-175.625525,57.769261],[-181.911904,54.676557],[-185.180751,52.875241],[-186.171957,51.865580],[-186.986268,50.601102],[-187.537820,49.246453],[-187.740751,47.966281],[-187.557300,46.555620],[-187.034435,44.973742],[-186.213386,43.319911],[-185.135385,41.693391],[-182.893627,39.126522],[-179.572243,35.717905],[-176.147099,32.435390],[-173.594057,30.246831],[-171.772601,29.125298],[-169.766360,28.276300],[-167.689251,27.738527],[-165.655193,27.550671],[-163.716101,27.672944],[-161.404488,28.023275],[-158.853398,28.576928],[-156.195874,29.309171],[-152.195612,30.687004],[-145.697261,33.232208],[-119.740751,44.032041],[-80.874021,60.302990],[-55.740751,70.684751],[-15.900751,86.366281],[-7.260751,89.317481],[-3.291388,90.692574],[0.029168,92.132945],[2.738037,93.656841],[4.872339,95.282511],[6.491082,96.947912],[7.592051,98.575713],[8.219891,100.251234],[8.419249,102.059791],[8.281448,103.785467],[7.950139,105.279791],[7.244646,106.829576],[6.182653,108.517033],[4.792555,110.301957],[3.102749,112.144141],[-0.172666,115.069073],[-1.855661,116.270736],[-3.582824,117.306137],[-5.364642,118.180985],[-7.211598,118.900985],[-9.134176,119.471845],[-11.142861,119.899271],[-13.762748,120.215675],[-16.420466,120.243388],[-19.173507,119.967912],[-22.079361,119.374751],[-25.195520,118.449407],[-28.579478,117.177384],[-32.288724,115.544184],[-36.380751,113.535311],[-43.755489,109.799912],[-49.971436,106.829843],[-69.889481,98.153451],[-103.626503,83.907598],[-112.651088,80.303908],[-116.756001,78.919311],[-117.785812,78.944388],[-118.801626,79.343662],[-119.713865,80.065063],[-120.432951,81.056521],[-120.879118,82.638280],[-120.948431,84.973453],[-120.643014,88.013698],[-119.964991,91.710671],[-118.623561,98.590671],[-118.137687,101.138715],[-117.540194,103.335576],[-116.847975,105.128974],[-116.077921,106.466631],[-114.967832,107.593729],[-113.427537,108.639937],[-111.645594,109.497222],[-109.810561,110.057551],[-103.250561,110.903501],[-95.972651,111.748528],[-88.535319,112.790455],[-81.120216,113.993716],[-73.908991,115.322746],[-67.083294,116.741981],[-60.824774,118.215855],[-55.315084,119.708803],[-50.735871,121.185261],[-48.045933,122.262413],[-45.552540,123.489039],[-43.259992,124.861702],[-41.172594,126.376962],[-39.294649,128.031381],[-37.630457,129.821522],[-36.184324,131.743944],[-34.960551,133.795211],[-34.029879,135.852237],[-33.383423,137.936689],[-33.021027,140.043420],[-32.942541,142.167281],[-33.147809,144.303125],[-33.636679,146.445805],[-34.408997,148.590173],[-35.464611,150.731081],[-36.816551,152.983840],[-38.022503,154.566016],[-39.275312,155.689845],[-40.767821,156.567561],[-41.966118,157.110223],[-43.028762,157.443648],[-45.843781,157.735051],[-48.559742,157.718817],[-50.921591,157.497481],[-53.044988,157.029816],[-55.359690,156.338853],[-60.435889,154.343881],[-65.895952,151.626269],[-71.485641,148.299721],[-74.013899,146.851112],[-77.115211,145.399291],[-80.801327,143.939212],[-85.084001,142.465831],[-91.421183,140.640985],[-97.850091,139.337321],[-102.187718,138.892733],[-107.450569,138.745185],[-112.545846,138.894455],[-116.380751,139.340321],[-120.126638,140.258143],[-123.404937,141.370673],[-126.410380,142.755292],[-129.337701,144.489381],[-135.101458,149.332840],[-147.373736,160.268501],[-164.279415,175.607809],[-183.943378,193.662211],[-194.213836,203.336577],[-196.765187,206.007411],[-198.521141,208.155841],[-201.570758,212.543761],[-203.689022,216.371303],[-204.414717,218.108897],[-204.926560,219.747155],[-205.230878,221.299660],[-205.334002,222.780001],[-205.163430,224.726031],[-204.612098,226.312996],[-203.641280,227.614390],[-202.212252,228.703711],[-200.504876,229.514892],[-198.712927,230.070211],[-194.537827,230.526825],[-187.100751,231.100731],[-176.722932,231.611963],[-164.860751,231.772001],[-157.016190,231.731578],[-151.232635,231.551558],[-146.423138,231.174862],[-141.500751,230.544411],[-137.865002,230.194936],[-134.310772,230.176171],[-131.151531,230.475038],[-128.700751,231.078461],[-126.920451,231.984265],[-125.348597,233.220795],[-124.139018,234.641109],[-123.445541,236.098271],[-123.181567,238.157656],[-123.056171,241.217691],[-123.157892,244.346051],[-123.533306,247.097291],[-124.216234,249.640541],[-125.240501,252.144931],[-126.523167,254.300650],[-128.207529,256.329927],[-130.123542,258.055426],[-132.101161,259.299811],[-133.906903,260.005557],[-136.599239,260.835829],[-143.881036,262.692591],[-152.421242,264.515370],[-160.694546,265.949441],[-167.432601,266.763606],[-174.721638,267.355800],[-181.678681,267.669854],[-187.420751,267.649601]]);
    linear_extrude(height=h)
      polygon([[-3.430551,78.277131],[-4.835804,77.626569],[-6.249308,76.607860],[-7.573296,75.303946],[-8.710001,73.797771],[-10.203882,70.408238],[-12.505971,63.873101],[-15.260751,55.309451],[-15.842921,53.581923],[-17.340209,49.890478],[-21.584821,40.190671],[-26.470478,30.054440],[-33.895891,15.120961],[-40.965907,0.877713],[-44.997111,-7.599039],[-47.158393,-12.948722],[-49.161285,-18.503334],[-50.998952,-24.237070],[-52.664558,-30.124120],[-54.151268,-36.138679],[-55.452245,-42.254938],[-56.560654,-48.447091],[-57.469661,-54.689329],[-58.232296,-61.107930],[-58.678786,-66.593499],[-58.888485,-72.526983],[-58.940751,-80.289329],[-58.827996,-91.112143],[-58.602728,-93.861356],[-58.189911,-96.449329],[-57.138354,-101.400628],[-55.813503,-106.097072],[-54.207112,-110.555332],[-52.310933,-114.792079],[-50.116720,-118.823984],[-47.616227,-122.667719],[-44.801206,-126.339953],[-41.663411,-129.857359],[-39.131381,-132.368095],[-36.438815,-134.784154],[-33.588545,-137.103539],[-30.583404,-139.324255],[-27.426227,-141.444307],[-24.119847,-143.461699],[-20.667097,-145.374435],[-17.070811,-147.180519],[-10.433456,-150.055803],[-7.207396,-151.223284],[-4.024709,-152.215919],[-0.871620,-153.037653],[2.265651,-153.692433],[5.400882,-154.184203],[8.547849,-154.516909],[12.065649,-154.659374],[15.523986,-154.505558],[19.005432,-154.048072],[22.592559,-153.279529],[25.923925,-152.325187],[29.232108,-151.148087],[32.531124,-149.740752],[35.834989,-148.095704],[39.157719,-146.205467],[42.513328,-144.062562],[45.915833,-141.659512],[49.379249,-138.988839],[53.082912,-135.851433],[56.819799,-132.454459],[60.139855,-129.107939],[63.849898,-125.077204],[67.450184,-120.921865],[70.440969,-117.201529],[72.415640,-114.473803],[74.230657,-111.703755],[75.876443,-108.910835],[77.343424,-106.114493],[78.622024,-103.334178],[79.702667,-100.589339],[80.575777,-97.899426],[81.231779,-95.283889],[81.689272,-92.455029],[81.907377,-89.540579],[81.879155,-86.749144],[81.597669,-84.289329],[80.657328,-80.578913],[80.005888,-78.924055],[79.198928,-77.342199],[78.210444,-75.787920],[77.014429,-74.215795],[73.895789,-70.836309],[71.643862,-68.738634],[69.763669,-67.300855],[68.180401,-66.474058],[66.819249,-66.209329],[65.606994,-66.427501],[64.267592,-67.049739],[62.883448,-68.027627],[61.536969,-69.312749],[59.633551,-71.690375],[57.232058,-75.206554],[54.320369,-79.879975],[50.886359,-85.729329],[47.831582,-90.903699],[45.178784,-95.038254],[42.668321,-98.515787],[40.040549,-101.719089],[37.911887,-104.031577],[35.638810,-106.237634],[33.233759,-108.331397],[30.709175,-110.306999],[28.077500,-112.158575],[25.351175,-113.880258],[22.542641,-115.466183],[19.664339,-116.910484],[16.728712,-118.207296],[13.748199,-119.350753],[10.735243,-120.334989],[7.702284,-121.154139],[4.661764,-121.802337],[1.626124,-122.273716],[-1.392195,-122.562412],[-4.380751,-122.662559],[-7.594478,-122.570211],[-10.190413,-122.231092],[-12.561517,-121.565591],[-15.100751,-120.494099],[-17.096652,-119.393545],[-18.972258,-118.038669],[-20.719272,-116.439957],[-22.329397,-114.607898],[-23.794336,-112.552980],[-25.105791,-110.285690],[-26.255465,-107.816517],[-27.235061,-105.155949],[-28.304210,-101.123559],[-29.095350,-96.537362],[-29.607150,-91.479994],[-29.838282,-86.034089],[-29.787414,-80.282282],[-29.453216,-74.307206],[-28.834358,-68.191497],[-27.929511,-62.017789],[-26.412379,-54.462224],[-25.478602,-50.923222],[-24.356409,-47.330310],[-21.331955,-39.343466],[-16.909371,-29.223109],[-7.098371,-6.849329],[5.335951,21.780667],[12.414079,37.627791],[14.721618,42.829561],[16.077729,46.276331],[16.667402,48.702246],[17.132229,51.449641],[17.347943,54.364178],[17.120429,57.107851],[16.679375,59.448424],[16.042573,61.706218],[15.205075,63.890248],[14.161931,66.009527],[12.908191,68.073068],[11.438905,70.089885],[9.749125,72.068992],[7.833899,74.019401],[6.320342,75.361838],[4.831070,76.474999],[3.369014,77.357776],[1.937103,78.009061],[0.538266,78.427747],[-0.824566,78.612725],[-2.148465,78.562889],[-3.430501,78.277131]]);
    difference()
    {
       linear_extrude(height=h)
         polygon([[-224.948451,44.266121],[-225.691605,43.231446],[-226.288320,41.985901],[-226.638049,40.367345],[-226.756704,38.325035],[-226.643920,36.123910],[-226.299330,34.028911],[-225.465463,31.189345],[-224.041700,27.674277],[-221.703853,22.756966],[-218.127732,15.710671],[-202.312065,-15.391047],[-197.624870,-24.925941],[-196.033356,-28.549929],[-196.965059,-28.832950],[-198.823081,-29.131369],[-200.759248,-29.468978],[-202.264542,-29.929394],[-203.213245,-30.461758],[-203.439589,-30.739026],[-203.479641,-31.015209],[-175.962396,-89.074519],[-152.362984,-138.384640],[-148.451052,-146.079483],[-147.496665,-147.667020],[-146.840335,-148.502319],[-145.174446,-150.049947],[-143.425857,-151.164923],[-141.546515,-151.871372],[-139.488367,-152.193419],[-137.452029,-152.166145],[-135.603481,-151.861829],[-134.272401,-151.570938],[-133.511711,-151.529399],[-128.338519,-161.328595],[-116.398641,-184.697369],[-103.938514,-209.068835],[-97.514531,-221.278765],[-93.242942,-227.905965],[-88.466046,-234.317127],[-83.011427,-240.728321],[-76.706671,-247.355618],[-71.696083,-252.223172],[-67.053394,-256.368470],[-62.413606,-260.101292],[-57.411721,-263.731416],[-53.151992,-266.566755],[-48.736607,-269.270732],[-44.191503,-271.830523],[-39.542619,-274.233304],[-34.815892,-276.466248],[-30.037260,-278.516532],[-25.232660,-280.371331],[-20.428031,-282.017820],[-13.327901,-284.091512],[-6.048981,-285.819570],[1.382735,-287.199089],[8.941256,-288.227160],[16.600588,-288.900878],[24.334739,-289.217335],[32.117717,-289.173626],[39.923529,-288.766843],[46.768483,-288.120058],[53.312137,-287.232174],[59.582560,-286.095964],[65.607818,-284.704204],[71.415979,-283.049668],[77.035109,-281.125131],[82.493277,-278.923366],[87.818549,-276.437150],[94.424679,-272.852856],[100.491894,-268.942205],[106.204157,-264.575929],[111.745429,-259.624760],[115.944999,-255.339767],[119.900379,-250.772282],[123.583180,-245.957176],[126.965009,-240.929321],[129.258181,-236.967914],[131.850444,-232.021181],[134.281031,-227.003226],[136.089169,-222.828153],[138.529452,-216.087883],[140.605251,-209.316691],[142.341136,-202.426521],[143.761679,-195.329319],[144.926253,-187.980984],[145.654952,-181.202250],[146.046439,-173.738709],[146.199379,-164.335949],[146.334389,-155.250867],[146.548629,-151.317009],[150.938709,-149.257789],[165.018363,-142.885709],[180.759949,-135.348159],[194.451808,-128.462641],[205.669379,-122.440557],[214.954493,-116.978411],[222.848979,-111.772709],[228.263026,-107.672752],[230.109736,-106.075546],[230.819249,-105.242039],[230.529253,-104.859249],[229.822327,-104.442192],[228.943061,-104.106880],[228.136049,-103.969329],[226.825117,-104.527620],[224.645069,-106.026389],[219.849975,-109.537057],[214.467129,-113.204089],[208.532275,-117.006317],[202.081156,-120.922573],[195.149514,-124.931690],[187.773092,-129.012500],[171.828879,-137.304529],[154.984293,-145.487102],[149.239390,-148.106762],[146.679409,-149.089319],[146.205702,-148.961256],[145.904389,-148.521874],[145.745547,-147.688382],[145.699249,-146.377989],[145.699249,-144.679009],[148.819249,-143.320759],[161.857341,-137.506599],[173.699249,-131.801819],[181.381373,-127.916937],[188.021958,-124.371390],[194.134789,-120.881758],[200.233649,-117.164619],[205.916434,-113.469887],[211.164231,-109.788877],[215.871632,-106.198575],[219.933229,-102.775969],[221.045851,-101.624129],[221.113764,-101.288036],[220.934029,-100.971249],[220.600956,-100.661861],[220.212819,-100.490615],[219.190841,-100.589213],[217.707067,-101.320366],[215.600469,-102.737399],[205.371561,-109.650885],[193.827789,-116.850999],[182.617710,-123.297330],[171.596971,-129.169449],[160.442898,-134.632294],[148.832819,-139.850799],[143.477484,-142.038290],[142.112297,-142.455086],[141.389779,-142.503369],[140.751046,-142.271647],[140.405839,-141.976662],[140.360506,-141.628850],[140.621389,-141.238649],[143.114401,-139.906100],[148.493359,-137.305099],[160.320744,-131.418514],[173.219249,-124.355299],[186.067052,-116.843724],[194.179249,-111.873539],[194.177249,-111.817224],[193.935249,-111.903345],[192.899249,-112.429869],[176.300365,-121.461298],[160.719016,-129.765198],[148.307783,-136.207603],[141.219249,-139.654549],[138.224529,-140.785582],[136.419249,-141.174369],[132.347782,-140.672995],[129.199189,-140.055919],[129.099200,-139.845559],[129.201385,-139.588022],[130.118317,-138.865892],[135.544689,-136.134719],[151.149758,-128.528618],[158.290205,-124.855054],[163.619249,-121.959549],[173.819498,-115.813311],[178.451939,-112.772689],[182.771812,-109.754294],[186.778533,-106.758550],[190.471517,-103.785877],[193.850181,-100.836700],[196.913939,-97.911439],[201.336236,-93.197590],[202.564588,-91.661166],[202.883759,-90.967179],[202.243407,-91.126430],[200.965779,-91.771269],[198.062138,-93.264919],[194.389934,-94.961590],[191.096661,-96.352617],[189.329809,-96.929329],[188.725742,-96.773504],[188.355599,-96.398859],[188.327332,-95.465118],[188.545169,-93.965059],[188.838769,-91.964489],[184.579249,-94.442239],[178.140217,-98.320680],[171.336258,-102.214278],[164.218268,-106.097100],[156.837144,-109.943214],[149.243784,-113.726688],[141.489083,-117.421590],[133.623939,-121.001988],[125.699249,-124.441949],[117.311294,-127.889603],[108.853783,-131.206973],[102.129460,-133.703676],[98.941069,-134.689329],[98.507517,-134.575943],[98.412529,-134.289329],[100.765533,-132.831829],[106.245039,-129.889329],[117.669602,-123.734335],[121.769519,-121.366207],[123.939249,-119.951359],[124.739249,-119.290799],[123.619249,-119.831829],[105.859249,-129.420089],[89.219249,-138.467319],[80.259249,-141.355199],[67.478958,-145.396336],[56.210456,-148.764042],[45.126350,-151.841029],[32.899249,-155.010009],[17.290399,-158.794530],[2.018299,-162.175358],[-13.173326,-165.206437],[-28.540751,-167.941709],[-44.125276,-170.460878],[-57.617661,-172.287279],[-66.370291,-173.532189],[-63.949544,-180.110728],[-57.910851,-195.708609],[-49.295701,-217.729322],[-48.038231,-217.837661],[-43.260751,-217.574982],[-34.329486,-216.352774],[-24.453644,-214.476551],[-13.692836,-211.963416],[-2.106676,-208.830475],[10.245225,-205.094832],[23.303255,-200.773592],[37.007800,-195.883859],[51.299249,-190.442739],[64.568248,-185.100382],[78.617658,-179.186410],[92.913096,-172.930268],[106.920179,-166.561399],[116.738609,-162.209319],[117.133348,-162.398279],[117.368978,-162.872688],[117.410424,-163.493840],[117.222609,-164.123029],[115.675391,-165.212095],[111.902470,-167.256503],[99.403381,-173.392954],[83.173065,-180.895598],[66.659249,-188.127649],[52.659580,-193.850848],[38.835364,-199.122937],[25.264541,-203.919787],[12.025053,-208.217266],[-0.805161,-211.991242],[-13.148159,-215.217585],[-24.926003,-217.872165],[-36.060751,-219.930848],[-44.300751,-221.122547],[-46.946714,-221.536097],[-47.445487,-221.756427],[-47.580751,-222.037677],[-47.463251,-222.569428],[-47.180751,-223.104595],[-46.847012,-223.386583],[-46.166374,-223.488563],[-42.351761,-223.172315],[-35.582209,-222.307304],[-28.358696,-221.095833],[-20.593712,-219.521638],[-12.199751,-217.568456],[0.877590,-214.088339],[14.416278,-209.966516],[28.395820,-205.210975],[42.795722,-199.829704],[57.595489,-193.830690],[72.774627,-187.221919],[88.312642,-180.011380],[104.189039,-172.207059],[113.610401,-167.570263],[116.016976,-166.507093],[116.922389,-166.264449],[117.016262,-167.738298],[116.735074,-170.984154],[116.172487,-175.176376],[115.422159,-179.489319],[113.924159,-186.212062],[112.040629,-192.609319],[110.000737,-198.364503],[107.669388,-203.888054],[105.054347,-209.167426],[102.163377,-214.190074],[99.004244,-218.943452],[95.584711,-223.415013],[91.912545,-227.592211],[87.995509,-231.462501],[85.187917,-233.953202],[82.445628,-236.183275],[79.584215,-238.295638],[76.419249,-240.433208],[73.132252,-242.473197],[69.756314,-244.372402],[66.279899,-246.135784],[62.691472,-247.768303],[58.979499,-249.274917],[55.132444,-250.660588],[51.138772,-251.930274],[46.986949,-253.088935],[40.484884,-254.607572],[33.833397,-255.793307],[26.806103,-256.680448],[19.176619,-257.303300],[13.364787,-257.522355],[8.196829,-257.295200],[2.250925,-256.657319],[-3.803143,-255.673824],[-9.881620,-254.360571],[-15.900751,-252.733414],[-21.287240,-251.022597],[-26.199361,-249.224057],[-30.983584,-247.201249],[-35.986381,-244.817629],[-39.933380,-242.758287],[-43.750425,-240.584102],[-47.449362,-238.286725],[-51.042034,-235.857809],[-54.540287,-233.289006],[-57.955964,-230.571967],[-61.300911,-227.698344],[-64.586971,-224.659790],[-69.150821,-220.031407],[-73.499511,-215.100941],[-77.622614,-209.883951],[-81.509701,-204.395994],[-85.150345,-198.652627],[-88.534120,-192.669409],[-91.650598,-186.461897],[-94.489351,-180.045649],[-109.288537,-150.049119],[-142.868242,-82.765649],[-192.336137,16.271351],[-194.421832,20.368600],[-196.596426,24.224706],[-198.824150,27.779454],[-201.069234,30.972631],[-203.163146,33.559323],[-205.554336,36.180592],[-207.968320,38.551288],[-210.130617,40.386261],[-213.178250,42.389271],[-216.316188,43.887185],[-219.405714,44.825732],[-220.888974,45.068283],[-222.308114,45.150641],[-223.932897,44.993355],[-224.445353,44.724914],[-224.948451,44.266091]]);
       translate([0, 0, -fudge])
         linear_extrude(height=h+2*fudge)
           polygon([[-35.814621,-174.211769],[-33.906093,-174.794442],[-32.134621,-175.531149],[-30.238373,-176.843140],[-28.027711,-178.813429],[-25.878497,-181.241477],[-24.460301,-183.649319],[-23.484038,-186.000833],[-22.801118,-188.320713],[-22.399903,-190.658973],[-22.268751,-193.065629],[-22.349287,-194.936476],[-22.588993,-196.744450],[-22.985016,-198.482165],[-23.534506,-200.142237],[-24.234608,-201.717280],[-25.082471,-203.199910],[-26.075243,-204.582742],[-27.210071,-205.858391],[-29.069792,-207.490988],[-30.773701,-208.615076],[-32.506138,-209.267363],[-34.434431,-209.765623],[-36.395168,-209.973681],[-38.339549,-209.845193],[-40.323236,-209.371630],[-42.401891,-208.544458],[-44.600291,-207.196988],[-46.779589,-205.301681],[-48.730256,-203.068017],[-50.242761,-200.705476],[-51.415303,-198.028525],[-52.209662,-195.275929],[-52.628087,-192.491444],[-52.672823,-189.718823],[-52.346119,-187.001819],[-51.650223,-184.384186],[-50.587381,-181.909678],[-49.159841,-179.622049],[-47.449348,-177.644853],[-45.545711,-176.088980],[-43.441111,-174.949172],[-41.127731,-174.220169],[-39.524789,-173.899290],[-38.380388,-173.791407],[-37.281381,-173.895905],[-35.814621,-174.212169]]);
    }
  }
}
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
