BorisFR/FourthInARow/modelisation/openscad Boris/logo_ia.scad

// Module names are of the form poly_<inkscape-path-id>().  As a result,
// you can associate a polygon in this OpenSCAD program with the corresponding
// SVG element in the Inkscape document by looking for the XML element with
// the attribute id="inkscape-path-id".

// fudge value is used to ensure that subtracted solids are a tad taller
// in the z dimension than the polygon being subtracted from.  This helps
// keep the resulting .stl file manifold.
fudge = 0.1;

module logo_ia(h) {
	l_ia_poly_path2258(1);
	l_ia_poly_rect2221(1);
	l_ia_poly_path2256(1);
}

module l_ia_poly_path2258(h)
{
  scale([25.4/90, -25.4/90, 1]) union()
  {
    linear_extrude(height=h)
      polygon([[-348.343370,-299.999997],[-429.329816,-151.807228],[47.100903,-151.807228],[48.804186,-155.933918],[50.655575,-159.981314],[52.651679,-163.946025],[54.789107,-167.824659],[57.064467,-171.613824],[59.474369,-175.310131],[62.015420,-178.910187],[64.684229,-182.410601],[67.477406,-185.807982],[70.391557,-189.098939],[73.423293,-192.280080],[76.569221,-195.348015],[79.825951,-198.299352],[83.190090,-201.130700],[86.658248,-203.838668],[90.227032,-206.419864],[93.893053,-208.870898],[97.652917,-211.188377],[101.503235,-213.368912],[105.440613,-215.409109],[109.461662,-217.305580],[113.562990,-219.054931],[117.741204,-220.653773],[121.992915,-222.098713],[126.314730,-223.386361],[130.703258,-224.513324],[135.155107,-225.476213],[139.666887,-226.271636],[144.235206,-226.896202],[148.856672,-227.346518],[153.527894,-227.619195],[158.245481,-227.710841],[162.963070,-227.619199],[167.634295,-227.346524],[172.255764,-226.896210],[176.824084,-226.271647],[181.335866,-225.476225],[185.787717,-224.513338],[190.176246,-223.386375],[194.498061,-222.098728],[198.749772,-220.653788],[202.927987,-219.054947],[207.029315,-217.305596],[211.050363,-215.409125],[214.987742,-213.368927],[218.838059,-211.188392],[222.597923,-208.870912],[226.263942,-206.419878],[229.832726,-203.838681],[233.300883,-201.130712],[236.665021,-198.299363],[239.921749,-195.348025],[243.067677,-192.280089],[246.099411,-189.098946],[249.013562,-185.807988],[251.806737,-182.410606],[254.475545,-178.910191],[257.016595,-175.310134],[259.426496,-171.613827],[261.701856,-167.824660],[263.839283,-163.946026],[265.835387,-159.981315],[267.686776,-155.933918],[269.390058,-151.807228],[429.216864,-151.807228],[348.230419,-299.999997],[-348.343370,-299.999997]]);
  }
}

module l_ia_poly_rect2221(h)
{
  scale([25.4/90, -25.4/90, 1]) union()
  {
    linear_extrude(height=h)
      polygon([[-595.368971,151.807228],[-676.468368,299.999997],[676.468368,299.999997],[595.368971,151.807228],[-595.368971,151.807228]]);
  }
}

module l_ia_poly_path2256(h)
{
  scale([25.4/90, -25.4/90, 1]) union()
  {
    linear_extrude(height=h)
      polygon([[-476.769574,-65.060240],[-557.868971,83.132529],[557.756019,83.132529],[476.769574,-65.060240],[269.390058,-65.060240],[267.686772,-60.933553],[265.835381,-56.886160],[263.839274,-52.921451],[261.701844,-49.042820],[259.426482,-45.253656],[257.016579,-41.557351],[254.475527,-37.957296],[251.806716,-34.456883],[249.013540,-31.059502],[246.099388,-27.768545],[243.067652,-24.587404],[239.921724,-21.519469],[236.664995,-18.568131],[233.300856,-15.736783],[229.832699,-13.028814],[226.263915,-10.447617],[222.597896,-7.996583],[218.838032,-5.679103],[214.987716,-3.498567],[211.050338,-1.458368],[207.029290,0.438103],[202.927964,2.187456],[198.749750,3.786299],[194.498041,5.231240],[190.176227,6.518888],[185.787700,7.645853],[181.335851,8.608743],[176.824072,9.404167],[172.255754,10.028733],[167.634289,10.479050],[162.963067,10.751727],[158.245481,10.843373],[153.527897,10.751724],[148.856678,10.479044],[144.235214,10.028724],[139.666898,9.404156],[135.155119,8.608731],[130.703271,7.645840],[126.314744,6.518874],[121.992930,5.231225],[117.741220,3.786283],[113.563006,2.187440],[109.461678,0.438087],[105.440629,-1.458384],[101.503250,-3.498583],[97.652932,-5.679118],[93.893067,-7.996597],[90.227046,-10.447631],[86.658260,-13.028827],[83.190102,-15.736794],[79.825961,-18.568142],[76.569231,-21.519478],[73.423301,-24.587412],[70.391565,-27.768553],[67.477412,-31.059508],[64.684235,-34.456888],[62.015424,-37.957300],[59.474372,-41.557354],[57.064470,-45.253658],[54.789108,-49.042821],[52.651680,-52.921452],[50.655575,-56.886160],[48.804186,-60.933553],[47.100903,-65.060240],[-476.769574,-65.060240]]);
  }
}

logo_ia(1);
