BorisFR/FourthInARow/FourthInARow/GO_serial.hpp

#ifndef GOserial_h
#define GOserial_h

#include "Global.hpp"
#include "GameOutput.hpp"

class GOserial : public GameOutput
{

	private:
		void traceLine();

	public:
		void showTouchSomething();
		void showChoosePlayersNumber();
		void showPlayerVsPlayer();
		void showPlayerVsIa();
		void showIaVsIa();
		void showDecideWhoStart();
		void showPlayer1Turn();
		void showPlayer2Turn();
		void showMatchDraw();
		void showWinPlayer1();
		void showWinPlayer2();

		void drawBoard(Board board); //Column board[BOARD_COLUMNS]);

};

#endif
